kasper201/StartWeekAvans25/PCB design/PCB_V2/PCB PNG/PCB-1.png

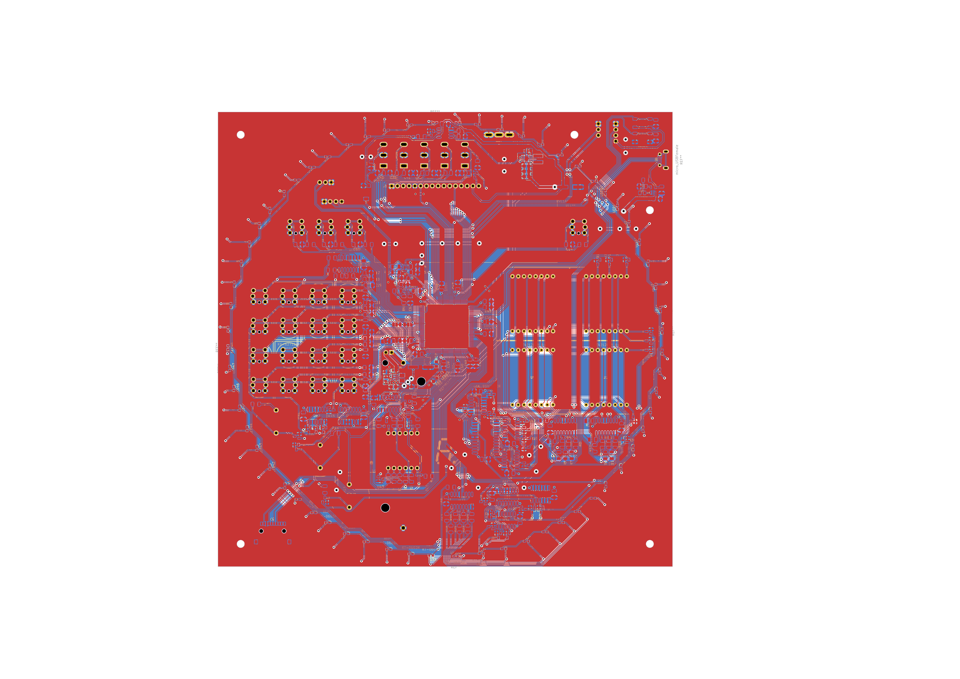
PCB design/PCB_V2/PCB PNG/PCB-1.png
