kasper201/StartWeekAvans25/PCB design/PCB_V2/Schematic PNG/PCB_V2-6.png

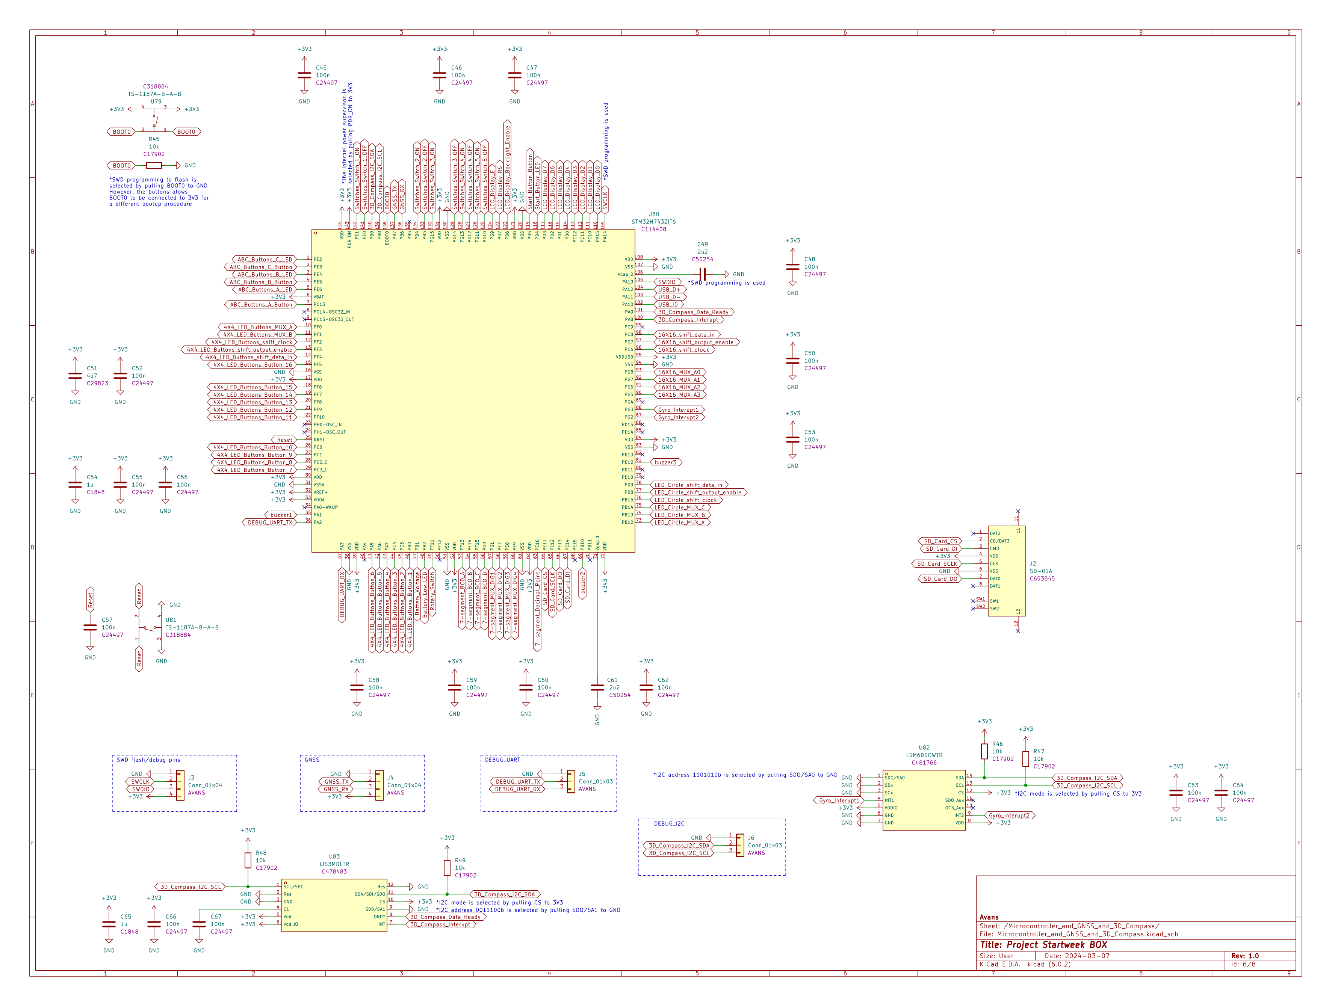
PCB design/PCB_V2/Schematic PNG/PCB_V2-6.png
