kasper201/StartWeekAvans25/Project/diagrams/games/Overview.png

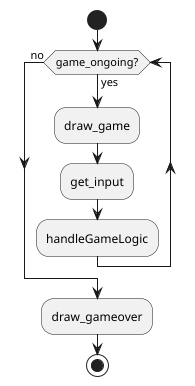
Project/diagrams/games/Overview.png
