kasper201/StartWeekAvans25/Project/diagrams/games/pokemonInPark/catchPokemonEvent.png

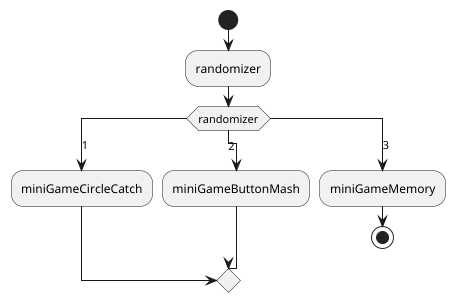
Project/diagrams/games/pokemonInPark/catchPokemonEvent.png
