kasper201/StartWeekAvans25/Project/diagrams/games/pokemonInPark/catchPokemonMiniGame.png

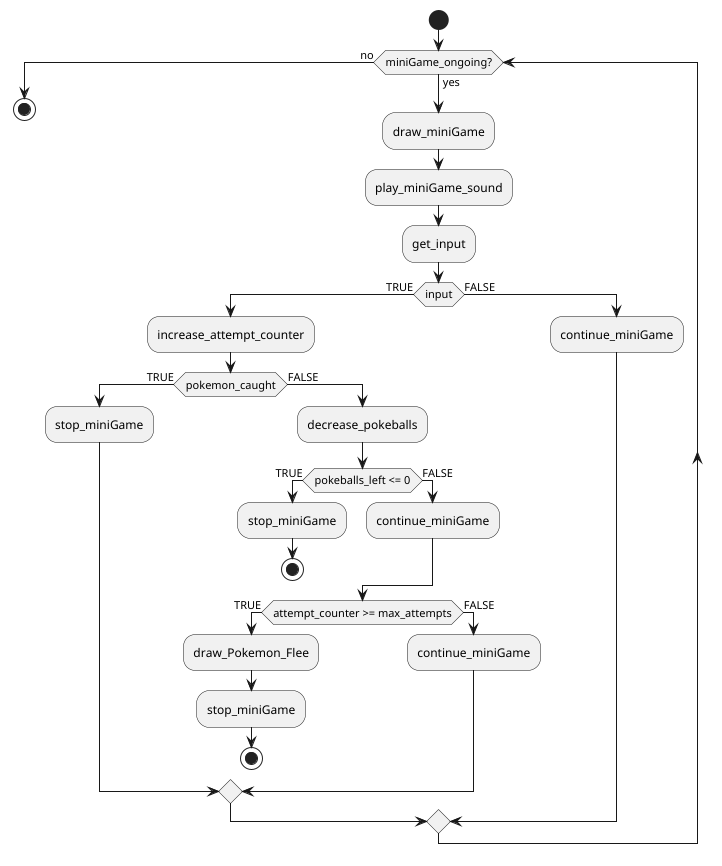
Project/diagrams/games/pokemonInPark/catchPokemonMiniGame.png
