kasper201/StartWeekAvans25/Project/diagrams/games/pokemonInPark/handleGameLogic.png

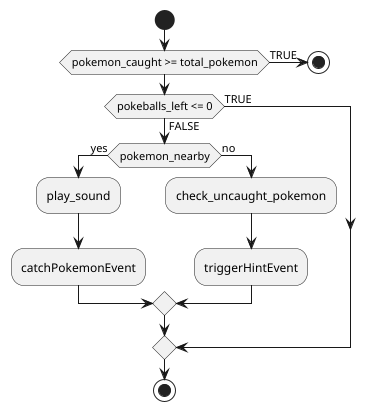
Project/diagrams/games/pokemonInPark/handleGameLogic.png
