kasper201/StartWeekAvans25/native_sim/hardware/inc/buzzers.h

#ifndef BUZZERS_h
#define BUZZERS_h
#include <stdint.h>
#include <stdio.h>

uint8_t buzzersInit();
uint8_t buzzerSetPwm(int aBuzzerNum, int aFreq);
uint8_t buzzerTurnOff(int aBuzzerNum);
uint8_t buzzersExit();


#endif /* BUZZERS_h */
