kasper201/StartWeekAvans25/native_sim/hardware/inc/genericGpio.h

#ifndef GENERIC_GPIO_H
#define GENERIC_GPIO_H

#include <zephyr/kernel.h>
#include <stdio.h>
#include <zephyr/drivers/gpio.h>

static const struct gpio_dt_spec switchon[5] = {
	GPIO_DT_SPEC_GET(DT_ALIAS(switches1on), gpios),
	GPIO_DT_SPEC_GET(DT_ALIAS(switches2on), gpios),
	GPIO_DT_SPEC_GET(DT_ALIAS(switches3on), gpios),
	GPIO_DT_SPEC_GET(DT_ALIAS(switches4on), gpios),
	GPIO_DT_SPEC_GET(DT_ALIAS(switches5on), gpios),
};

static const struct gpio_dt_spec switchoff[5] = {
	GPIO_DT_SPEC_GET(DT_ALIAS(switches1off), gpios),
	GPIO_DT_SPEC_GET(DT_ALIAS(switches2off), gpios),
	GPIO_DT_SPEC_GET(DT_ALIAS(switches3off), gpios),
	GPIO_DT_SPEC_GET(DT_ALIAS(switches4off), gpios),
	GPIO_DT_SPEC_GET(DT_ALIAS(switches5off), gpios),
};

static const struct gpio_dt_spec abcbutton[3] = {
	GPIO_DT_SPEC_GET(DT_ALIAS(abcbuttona), gpios),
	GPIO_DT_SPEC_GET(DT_ALIAS(abcbuttonb), gpios),
	GPIO_DT_SPEC_GET(DT_ALIAS(abcbuttonc), gpios),
};

static const struct gpio_dt_spec abcleds[3] = {
	GPIO_DT_SPEC_GET(DT_ALIAS(abcleda), gpios),
	GPIO_DT_SPEC_GET(DT_ALIAS(abcledb), gpios),
	GPIO_DT_SPEC_GET(DT_ALIAS(abcledc), gpios),
};

static const struct gpio_dt_spec startbutton	= GPIO_DT_SPEC_GET(DT_ALIAS(startbutton), gpios);
static const struct gpio_dt_spec startled		= GPIO_DT_SPEC_GET(DT_ALIAS(startled), gpios);

#ifndef HIGH
#define HIGH 1
#endif

#ifndef LOW
#define LOW 0
#endif

bool switchesConfig();
bool abcbuttonsConfig();
bool abcledsConfig();
bool startbuttonledConfig();

uint8_t switchesInit();
uint8_t abcbuttonsInit();
uint8_t abcledsInit();
uint8_t startbuttonledInit();

uint8_t switchesGet(uint8_t selectedswitch);
uint8_t abcbuttonsGet(char selectedbtn);
uint8_t abcledsSet(char selectedled,bool value);
uint8_t startbuttonGet();
uint8_t startledSet(bool value);

#endif // GENERIC_GPIO_H
